ctag/gestum/src/main.h

/**
 * Main header
 */

#ifndef MAIN_H
#define MAIN_H

// Include for Watchdog
#include <avr/wdt.h>
#include <avr/sleep.h>
#include <avr/io.h>
#include <stdio.h>
#include <avr/pgmspace.h>
#include <avr/interrupt.h>
#include <stdint.h>
#include <string.h>

#include "avr-i2c.h"
#include "avr-usart.h"
#include "avr-printf.h"
#include "bno055.h"
#include "linked-list.h"

#endif // MAIN_H
